reivaxy/SDRecorder/firmware/esp32/include/main.h

#pragma once


#include <Arduino.h>
#include <SD.h>
#include <SPI.h>
#include <driver/i2s.h>
#include <FS.h>
#include <WiFi.h>
#include "led.h"
#include <esp_sleep.h>
#include "sdCard.h"
#include "button.h"
#include <Preferences.h>
#include "server.h"
